nppc/MiniTX_ER9xrPro/Images/ProjectTX.png

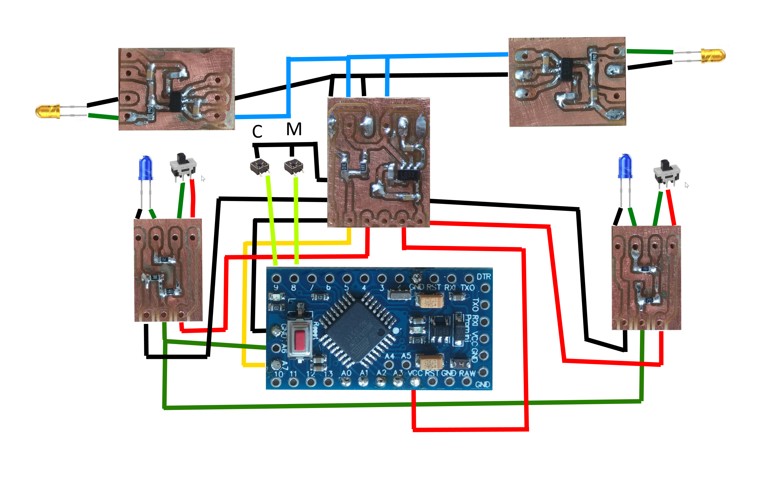
Images/ProjectTX.png
