nppc/MiniTX_ER9xrPro/KiCad/MiniTx_Er9XR_PRO.sch

## KiCad design KiCad/MiniTx_Er9XR_PRO.sch (2017-05-29, an earlier design)

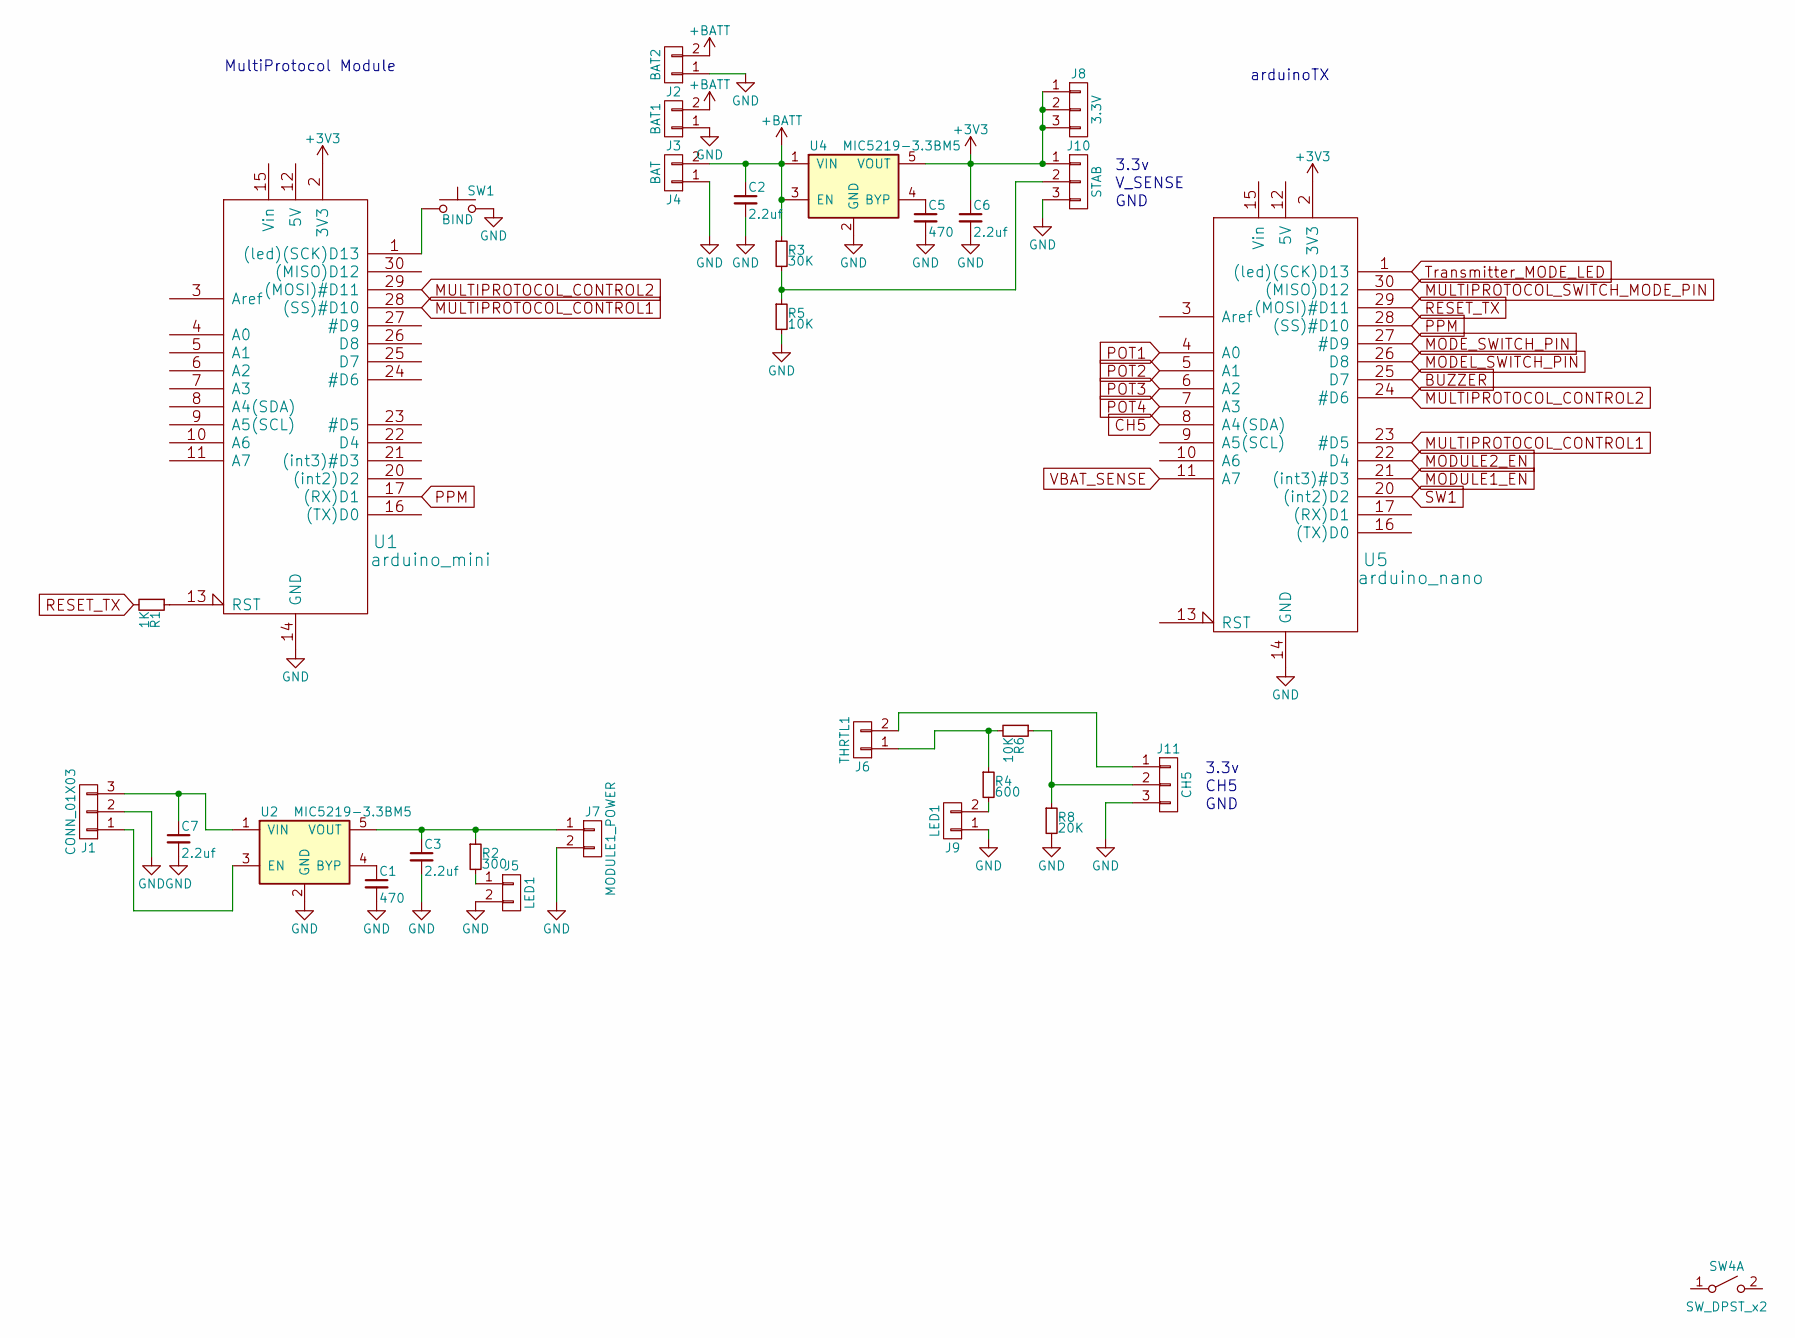
[picture p15: schematic MiniTx_Er9XR_PRO.sch]

Parts:
C1, C5: 470; C_0603_HandSoldering
C2, C3, C6, C7: 2.2uf; C_0603_HandSoldering
J1: CONN_01X03; PINHEAD1-3
J2: BAT2; PINHEAD1-2
J3: BAT1; PINHEAD1-2
J4: BAT; PINHEAD1-2
J5, J9: LED1; PINHEAD1-2
J6: THRTL1; PINHEAD1-2
J7: MODULE1_POWER; PINHEAD1-2
J8: 3.3V; PINHEAD1-3
J10: STAB; PINHEAD1-3
J11: CH5; PINHEAD1-3
R1: 1K
R2: 300; R_0603_HandSoldering
R3: 30K; R_0603_HandSoldering
R4: 600; R_0603_HandSoldering
R5, R6: 10K; R_0603_HandSoldering
R8: 20K; R_0603_HandSoldering
SW1: BIND
SW4: SW_DPST_x2
U1: arduino_mini
U2, U4: MIC5219-3.3BM5; SOT-23-5
U5: arduino_nano

Connections:
+3V3: C6.1, J8.1, J8.2, J8.3, J10.1, U1.2 (3V3), U4.5 (VOUT), U5.2 (3V3)
+BATT: C2.1, J2.2, J3.2, J4.2, R3.1, U4.1 (VIN), U4.3 (EN)
BUZZER: U5.25 (D7)
CH5: U5.8 (A4(SDA))
GND: C1.2, C2.2, C3.2, C5.2, C6.2, C7.2, J1.2, J2.1, J3.1, J4.1, J5.2, J7.2, J9.1, J10.3, J11.3, R5.2, R8.2, SW1.2, U1.14 (GND), U2.2 (GND), U4.2 (GND), U5.14 (GND)
MODEL_SWITCH_PIN: U5.26 (D8)
MODE_SWITCH_PIN: U5.27 (#D9)
MODULE1_EN: U5.21 ((int3)#D3)
MODULE2_EN: U5.22 (D4)
MULTIPROTOCOL_CONTROL1: U1.28 ((SS)#D10), U5.23 (#D5)
MULTIPROTOCOL_CONTROL2: U1.29 ((MOSI)#D11), U5.24 (#D6)
MULTIPROTOCOL_SWITCH_MODE_PIN: U5.30 ((MISO)D12)
unnamed: C1.1, U2.4 (BYP)
unnamed: C3.1, J7.1, R2.1, U2.5 (VOUT)
unnamed: C5.1, U4.4 (BYP)
unnamed: C7.1, J1.3, U2.1 (VIN)
unnamed: J1.1, U2.3 (EN)
unnamed: J5.1, R2.2
unnamed: J6.1, R4.1, R6.2
unnamed: J9.2, R4.2
unnamed: J10.2, R3.2, R5.1
unnamed: J6.2, J11.1
unnamed: J11.2, R6.1, R8.1
unnamed: R1.1, U1.13 (RST)
unnamed: SW1.1, U1.1 ((led)(SCK)D13)
POT1: U5.4 (A0)
POT2: U5.5 (A1)
POT3: U5.6 (A2)
POT4: U5.7 (A3)
PPM: U1.17 ((RX)D1), U5.28 ((SS)#D10)
RESET_TX: R1.2, U5.29 ((MOSI)#D11)
SW1: U5.20 ((int2)D2)
Transmitter_MODE_LED: U5.1 ((led)(SCK)D13)
VBAT_SENSE: U5.11 (A7)

Notes on the sheet:
MultiProtocol Module
arduinoTX
3.3v
CH5
GND
V_SENSE
